Akitoshi02/MyLifeIsPatate/Code source/Code source/main/SendData.ino

    byte yMSB=0, yLSB=0, xMSB=0, xLSB=0, zeroByte=128, Checksum=0;  
 
    void SendData(int Command, unsigned int yValue,unsigned int xValue){
    

      
      /* >=================================================================< 
          y = 01010100 11010100    (x & y are 2 Byte integers)
               yMSB      yLSB      send seperately -> reciever joins them
        >=================================================================<  */
       
        yLSB=lowByte(yValue);
        yMSB=highByte(yValue);
        xLSB=lowByte(xValue);
        xMSB=highByte(xValue);        
   
      
     /* >=================================================================< 
        Only the very first Byte may be a zero, this way allows the computer 
        to know that if a Byte recieved is a zero it must be the start byte.
        If data bytes actually have a value of zero, They are given the value 
        one and the bit in the zeroByte that represents that Byte is made 
        high.  
        >=================================================================< */   
        
       zeroByte = 128;                                   // 10000000
   
       if(yLSB==0){ yLSB=1; zeroByte=zeroByte+1;}        // Make bit 1 high 
       if(yMSB==0){ yMSB=1; zeroByte=zeroByte+2;}        // make bit 2 high
       if(xLSB==0){ xLSB=1; zeroByte=zeroByte+4;}        // make bit 3 high
       if(xMSB==0){ xMSB=1; zeroByte=zeroByte+8;}        // make bit 4 high
       

     /* >=================================================================< 
        Calculate the remainder of: sum of all the Bytes divided by 255 
        >=================================================================< */
        
       Checksum = (Command + yMSB + yLSB + xMSB + xLSB + zeroByte)%255;
       
       if( Checksum !=0 ){
        Serial.write(byte(0));            // send start bit 
        Serial.write(byte(Command));      // command eg: Which Graph is this data for
        
        Serial.write(byte(yMSB));         // Y value's most significant byte  
        Serial.write(byte(yLSB));         // Y value's least significant byte   
        Serial.write(byte(xMSB));         // X value's most significant byte  
        Serial.write(byte(xLSB));         // X value's least significant byte  
        
        Serial.write(byte(zeroByte));     // Which values have a zero value
        Serial.write(byte(Checksum));     // Error Checking Byte
       }
    }  
    


       
 void PlottArray(unsigned int Cmd,float Array1[],float Array2[]){
   
      SendData(Cmd+1, 1,1);                        // Tell PC an array is about to be sent                      
      delay(1);
      for(int x=0;  x < sizeOfArray;  x++){     // Send the arrays 
        SendData(Cmd, round(Array1[x]),round(Array2[x]));
        //delay(1);
      }
      
      SendData(Cmd+2, 1,1);                        // Confirm arrrays have been sent
    }
